Pyloupy/Pylou-s-Karambit/STLs/Tree Left Side.stl

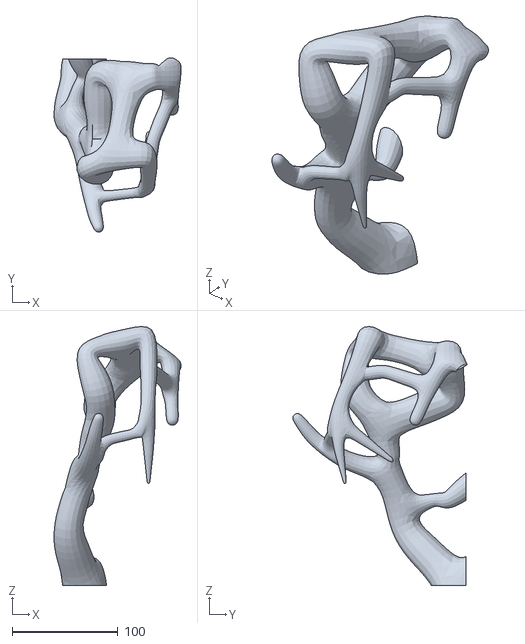
[picture p28: CAD file, 2026-06-09]
STLs/Tree Left Side.stl
120.2 x 164.9 x 245.1
